daverb/Wireless-GSM-Smoke-Alarm/Images/ReceiverDiagram.jpg

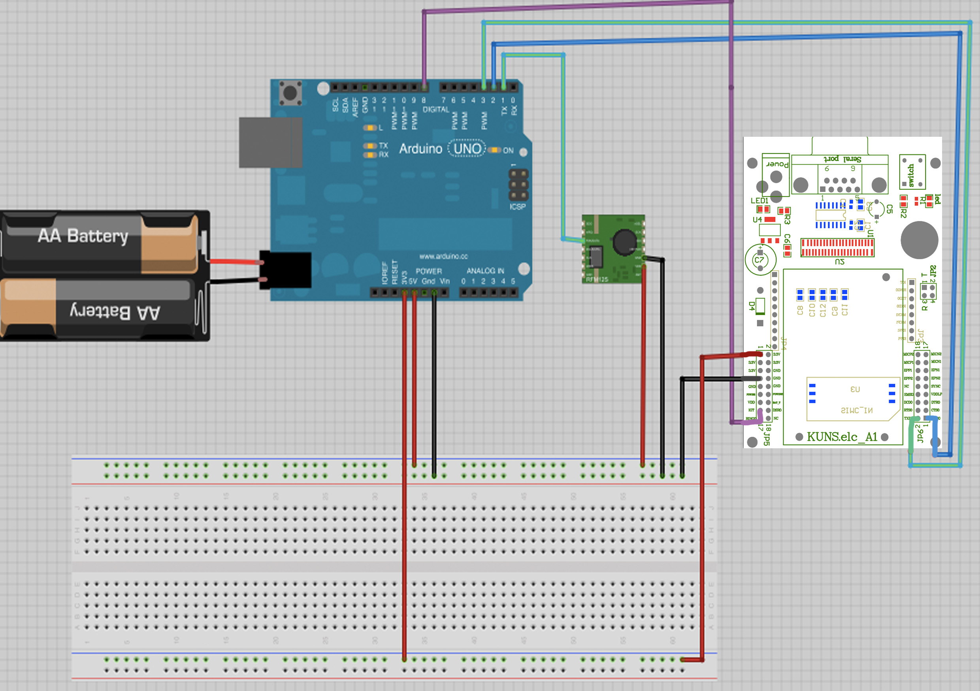
Images/ReceiverDiagram.jpg
