daverb/Wireless-GSM-Smoke-Alarm/Images/Photo 25-03-2013 13 33 46.png

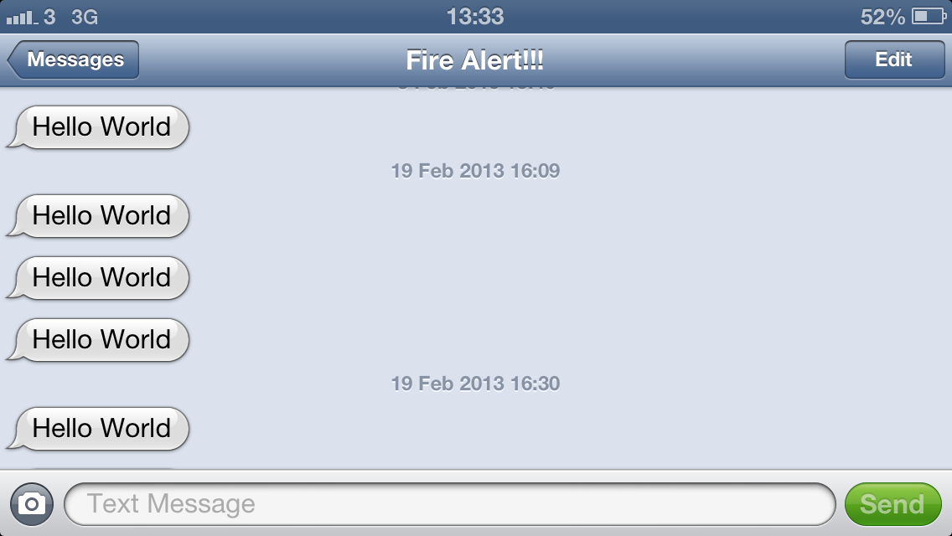
Images/Photo 25-03-2013 13 33 46.png
